pdumais/synth/modules/drum/bass_drum.png

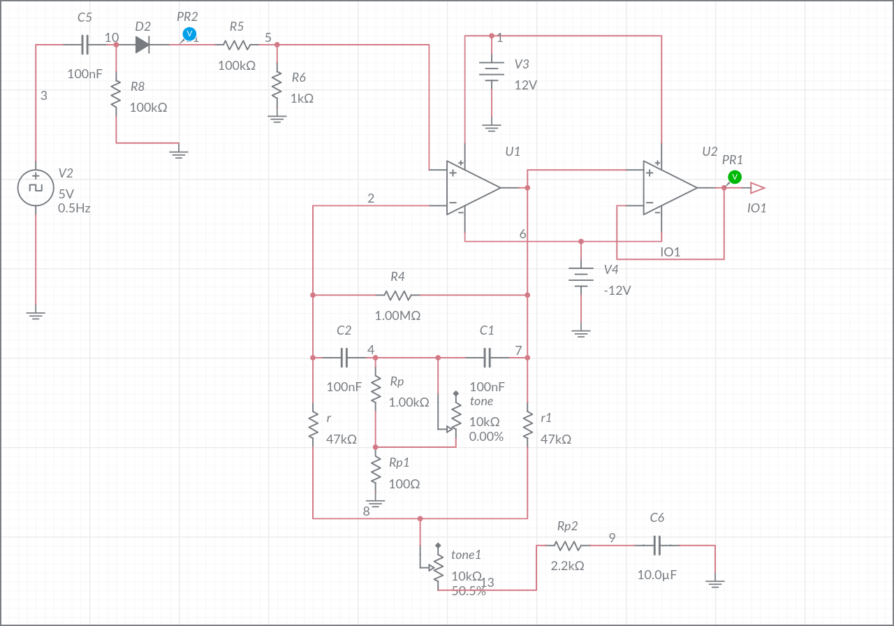
modules/drum/bass_drum.png
