pdumais/synth/modules/osc/circuit/VCO.png

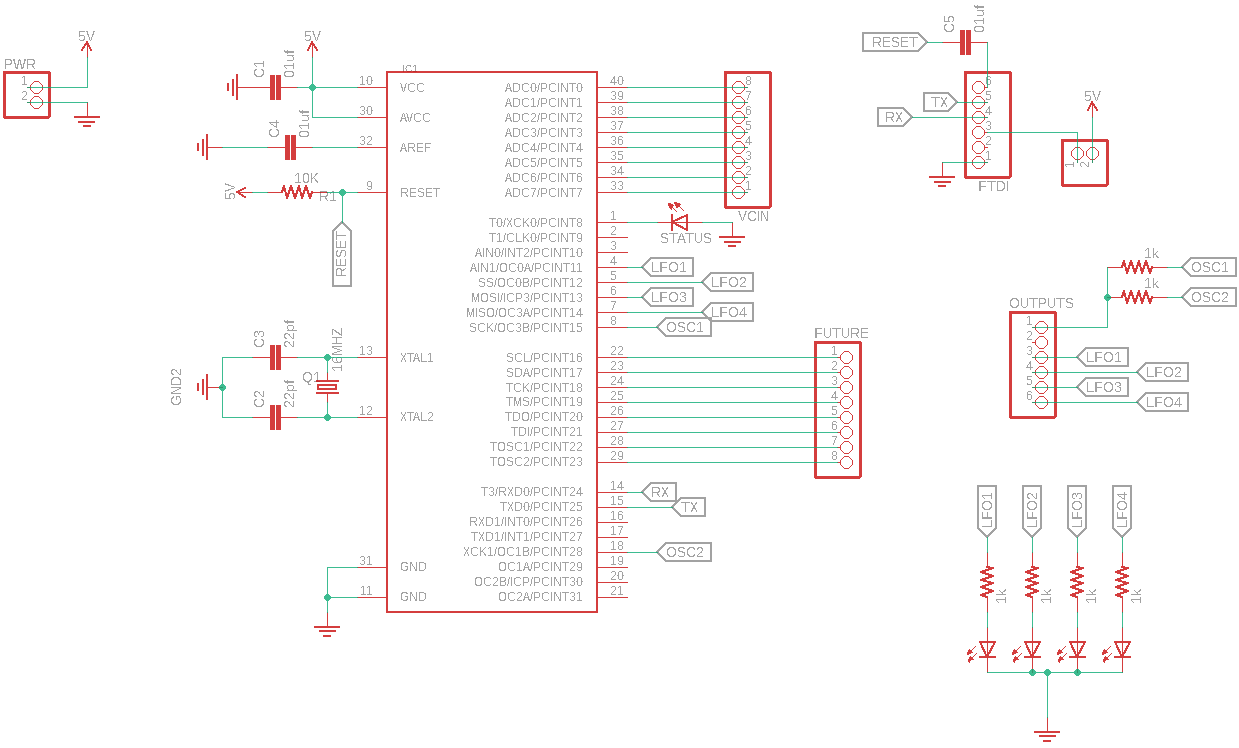
modules/osc/circuit/VCO.png
