pdumais/synth/modules/digipot/circuits/digipots.brd

## EAGLE design modules/digipot/circuits/digipots.brd (2022-02-02)

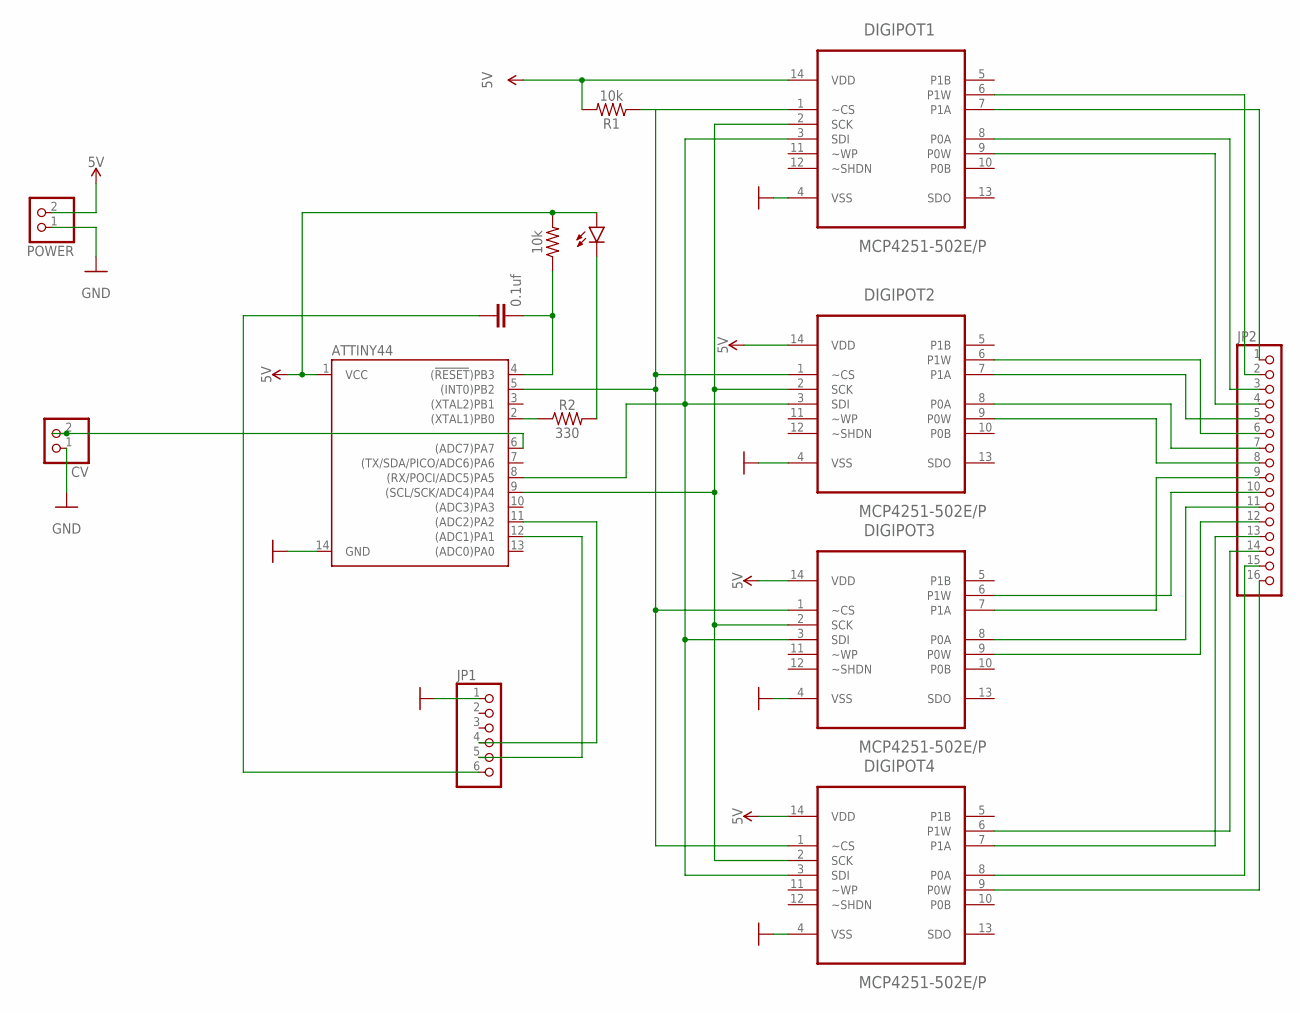
[picture p37: schematic digipots.sch]

Parts:
ATTINY44: ATTINY84ATTINY84-20PU; DIP14
C2: 0.1uf; C025-024X044
CV: PINHD-1X2; 1X02
D1: LED-5MM-KIT-NO-SILK; LED_5MM-KIT-NO-SILK
DIGIPOT1, DIGIPOT2, DIGIPOT3, DIGIPOT4: MCP4251-502E/P; DIP254P762X533-14
JP1: PINHD-1X6; 1X06
JP2: PINHD-1X16; 1X16
POWER: PINHD-1X2; 1X02
R1, R3: 10k; AXIAL-0.3
R2: 330; AXIAL-0.3

Connections:
5V: ATTINY44.1 (VCC), D1.A, DIGIPOT1.14 (VDD), DIGIPOT2.14 (VDD), DIGIPOT3.14 (VDD), DIGIPOT4.14 (VDD), POWER.2, R1.P$2 (2), R3.P$2 (2)
GND: ATTINY44.14 (GND), CV.1, DIGIPOT1.4 (VSS), DIGIPOT2.4 (VSS), DIGIPOT3.4 (VSS), DIGIPOT4.4 (VSS), JP1.1, POWER.1
unnamed: DIGIPOT4.9 (P0W), JP2.16
unnamed: DIGIPOT4.8 (P0A), JP2.15
unnamed: DIGIPOT4.6 (P1W), JP2.14
unnamed: DIGIPOT4.7 (P1A), JP2.13
unnamed: DIGIPOT3.9 (P0W), JP2.12
unnamed: DIGIPOT3.8 (P0A), JP2.11
unnamed: DIGIPOT3.6 (P1W), JP2.10
unnamed: DIGIPOT3.7 (P1A), JP2.9
unnamed: DIGIPOT2.9 (P0W), JP2.8
unnamed: DIGIPOT2.8 (P0A), JP2.7
unnamed: DIGIPOT2.7 (P1A), JP2.5
unnamed: DIGIPOT2.6 (P1W), JP2.6
unnamed: DIGIPOT1.9 (P0W), JP2.4
unnamed: DIGIPOT1.8 (P0A), JP2.3
unnamed: DIGIPOT1.7 (P1A), JP2.1
unnamed: DIGIPOT1.6 (P1W), JP2.2
unnamed: ATTINY44.5 ((INT0)PB2), DIGIPOT1.1 (~CS), DIGIPOT2.1 (~CS), DIGIPOT3.1 (~CS), DIGIPOT4.1 (~CS), R1.P$1 (1)
unnamed: ATTINY44.9 ((SCL/SCK/ADC4)PA4), DIGIPOT1.2 (SCK), DIGIPOT2.2 (SCK), DIGIPOT3.2 (SCK), DIGIPOT4.2 (SCK)
unnamed: ATTINY44.2 ((XTAL1)PB0), R2.P$1 (1)
unnamed: ATTINY44.8 ((RX/POCI/ADC5)PA5), DIGIPOT1.3 (SDI), DIGIPOT2.3 (SDI), DIGIPOT3.3 (SDI), DIGIPOT4.3 (SDI)
unnamed: D1.K (C), R2.P$2 (2)
unnamed: ATTINY44.4 ((!RESET!)PB3), C2.2, R3.P$1 (1)
unnamed: ATTINY44.12 ((ADC1)PA1), JP1.5
unnamed: C2.1, JP1.6
unnamed: ATTINY44.11 ((ADC2)PA2), JP1.4
unnamed: ATTINY44.6 ((ADC7)PA7), CV.2

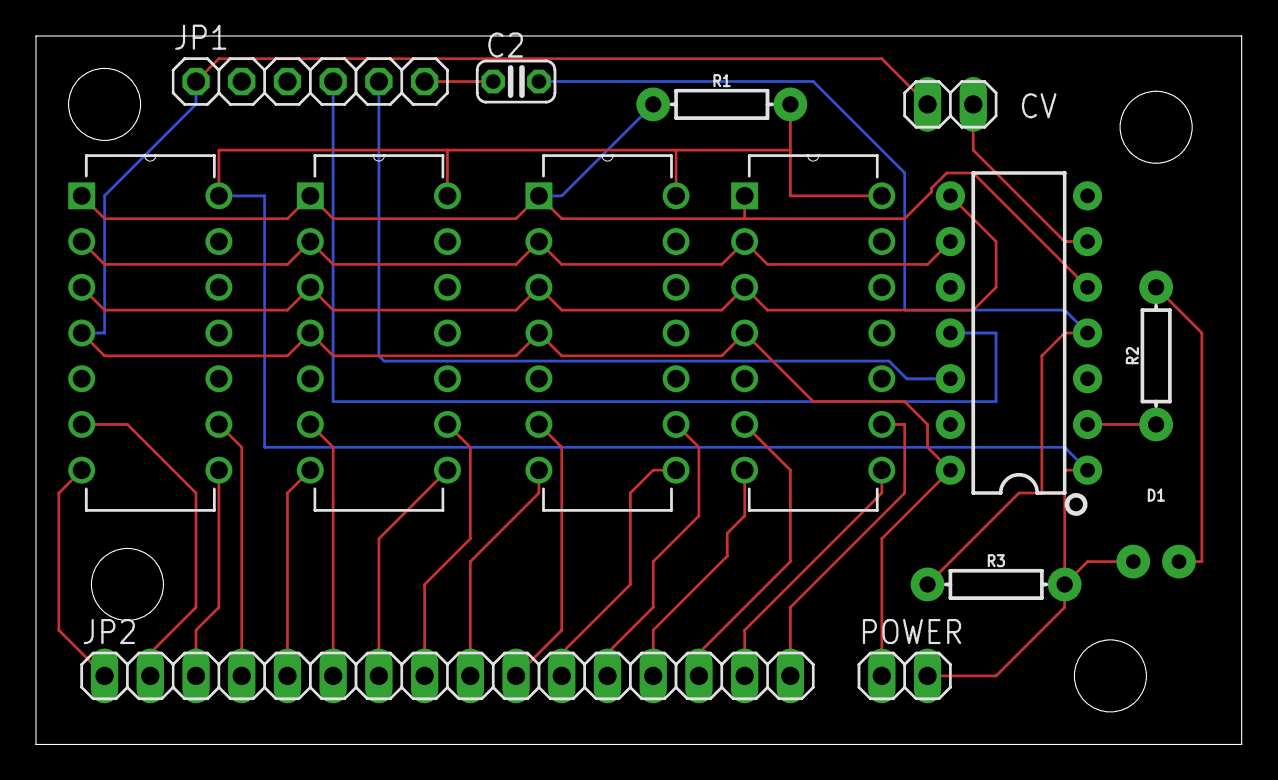
[picture p38: board digipots.brd from above]

Board: 2 copper layers, 67.0 x 39.4 mm, 14 parts (0 on the bottom side), 28 nets.
