pdumais/synth/circuits/waveshaper.brd

## EAGLE design circuits/waveshaper.brd (2022-01-30)

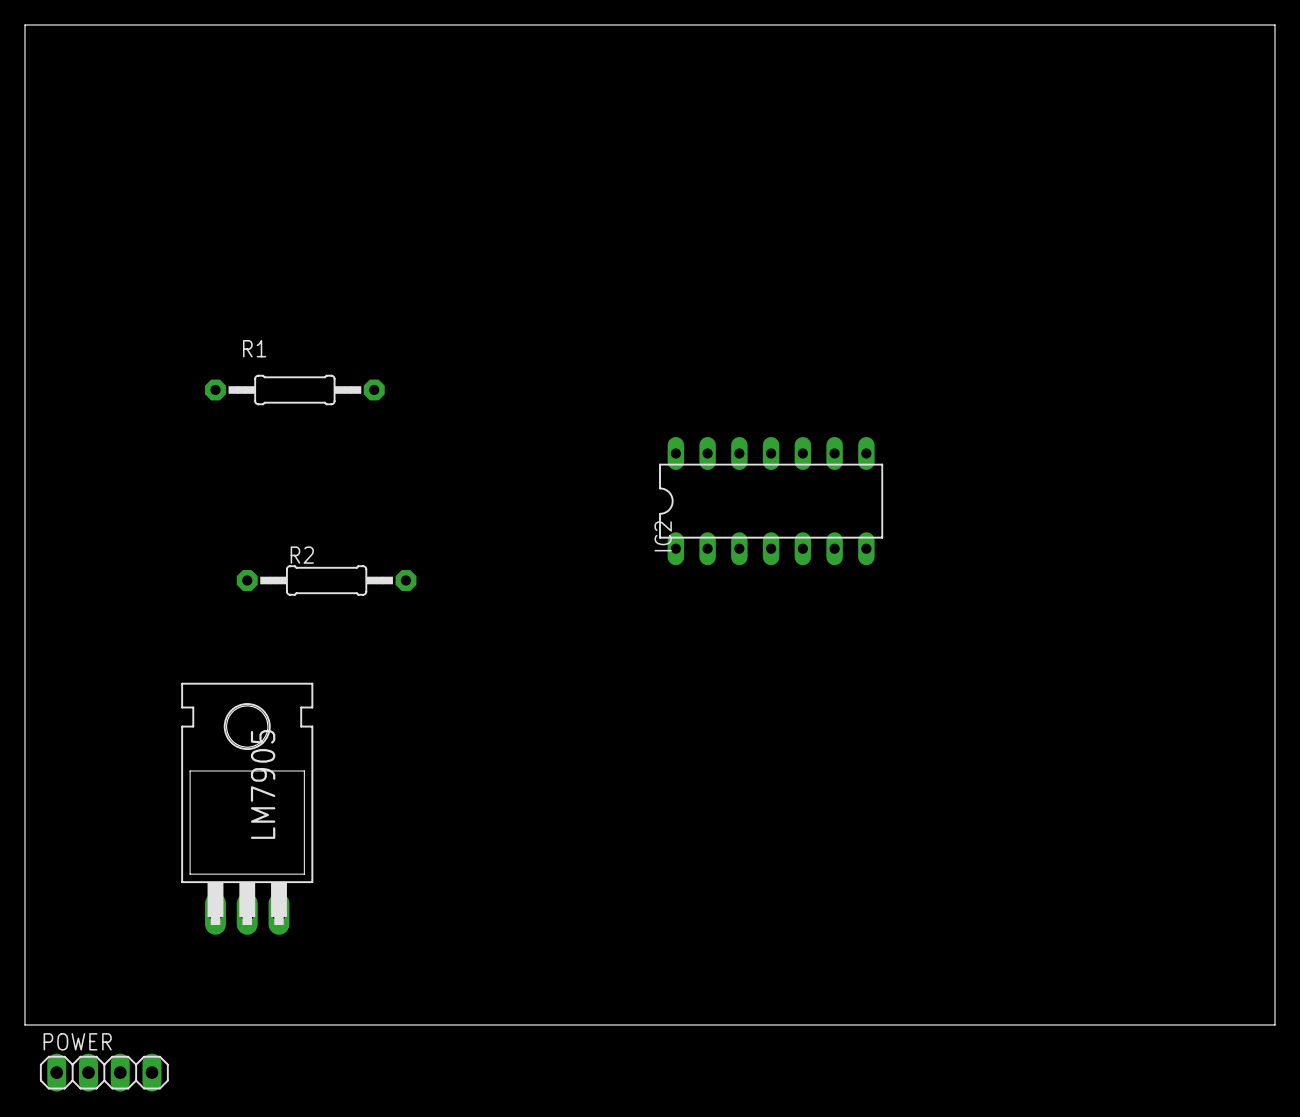
[picture p39: board circuits/waveshaper.brd from above]

Board: 2 copper layers, 100.0 x 80.0 mm, 5 parts (0 on the bottom side), 2 nets, no tracks yet.

Parts:
IC2: LM324N; DIL14
LM7905: TO220H
POWER: 1X04
R1, R2: 0207/12

Connections:
3.3V: LM7905.1, POWER.4
VDD: IC2.4, IC2.11, LM7905.2, LM7905.3, POWER.1, POWER.2, POWER.3
