pdumais/synth/general/circuits/cv-pots.sch

## EAGLE design general/circuits/cv-pots.sch (2022-02-20)

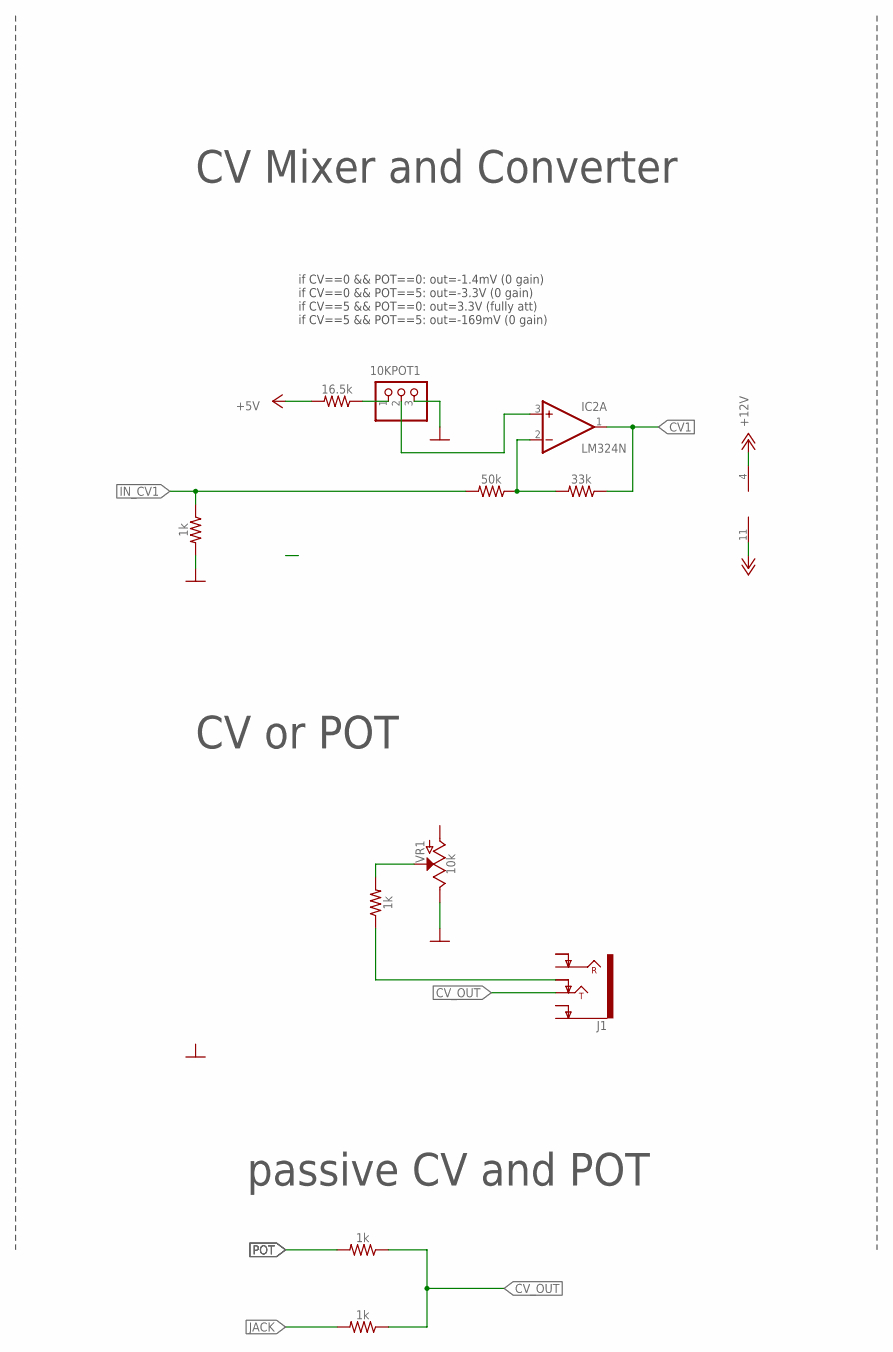
[picture p40: schematic cv-pots.sch]

Parts:
10KPOT1: PINHD-1X3; 1X03
IC2: LM324N; DIL14
J1: AUDIO_JACK_TRS_0.25"_PTH_RA; AUDIO_JACK_0.25"_TRS_PTH_RA
R1, R2, R3, R9: 1k; AXIAL-0.3
R18: 16.5k; AXIAL-0.3
R19: 50k; AXIAL-0.3
R20: 33k; AXIAL-0.3
VR1: 10k; POT-PTH-ALPS

Connections:
+5V: R18.P$2 (2)
+12V: IC2.4 (V+)
-12V: IC2.11 (V-)
CV1: IC2.1 (OUT), R20.P$1 (1)
CV_OUT: J1.TIP, R2.P$1 (1), R3.P$1 (1)
GND: 10KPOT1.3, R9.P$2 (2), VR1.P$1 (E)
IN_CV1: R9.P$1 (1), R19.P$2 (2)
JACK: R3.P$2 (2)
unnamed: R1.P$2 (2), VR1.P$2 (S)
unnamed: J1.TIP-NORM, R1.P$1 (1)
unnamed: 10KPOT1.2, IC2.3 (+IN)
unnamed: 10KPOT1.1, R18.P$1 (1)
unnamed: IC2.2 (-IN), R19.P$1 (1), R20.P$2 (2)
POT: R2.P$2 (2)

Notes on the sheet:
if CV==0 && POT==0: out=-1.4mV (0 gain) if CV==0 && POT==5: out=-3.3V (0 gain) if CV==5 && POT==0: out=3.3V (fully att) if CV==5 && POT==5: out=-169mV (0 gain)
CV Mixer and Converter
CV or POT
passive CV and POT
